hggh/binary-clock/3d/wood-connector.scad

cylinder(d=4.01, h=15, $fn=190);
